g7ltt/Celestron-GPS-WiFi-BT-Interface/PXL_20210731_114611073.jpg

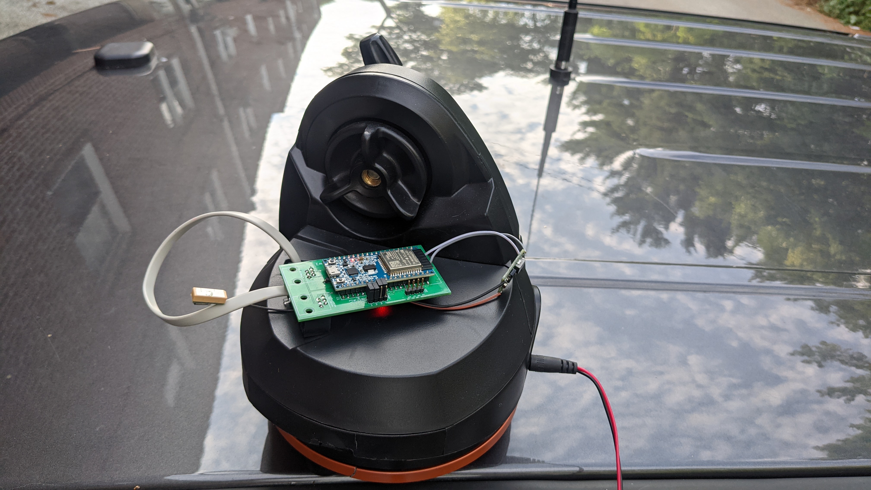
PXL_20210731_114611073.jpg
